Sabotax/Zdalne-ule/foldery pomocnicze/badania wytrzymalosci baterii/1.PNG

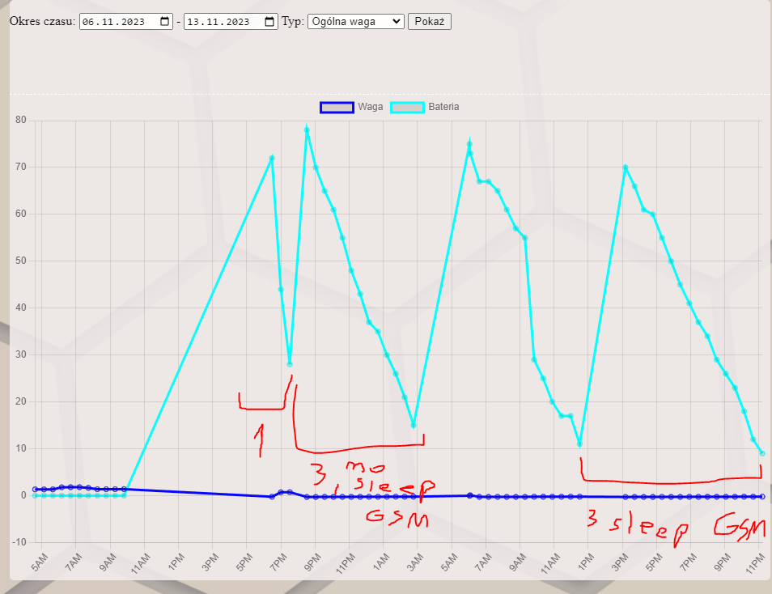
foldery pomocnicze/badania wytrzymalosci baterii/1.PNG
