Sabotax/Zdalne-ule/foldery pomocnicze/zdjecia readme/IMG_20230922_020804.jpg

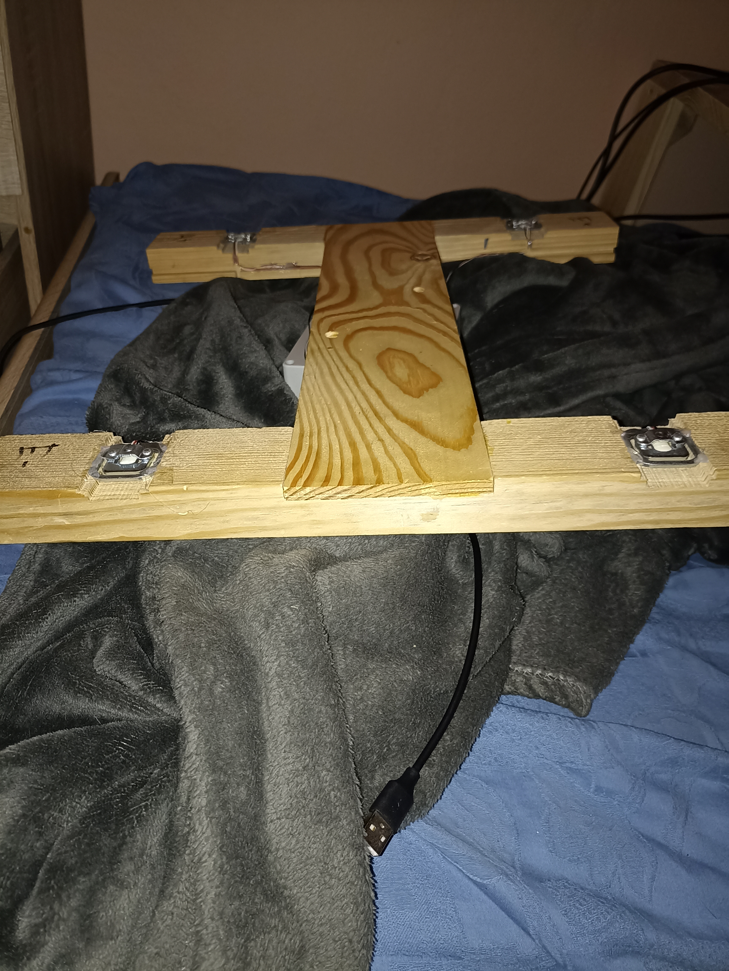
foldery pomocnicze/zdjecia readme/IMG_20230922_020804.jpg
