Sabotax/Zdalne-ule/kod_serwer/web/res/hex-pattern-1.jpg

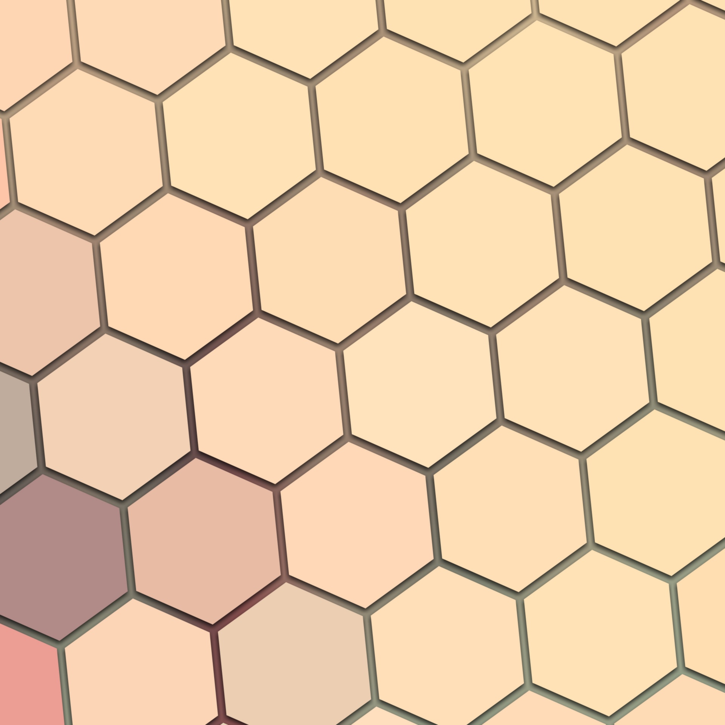
kod_serwer/web/res/hex-pattern-1.jpg
