Sabotax/Zdalne-ule/projekt PCB/esp-merged kicad/esp-merged_v1/2.png

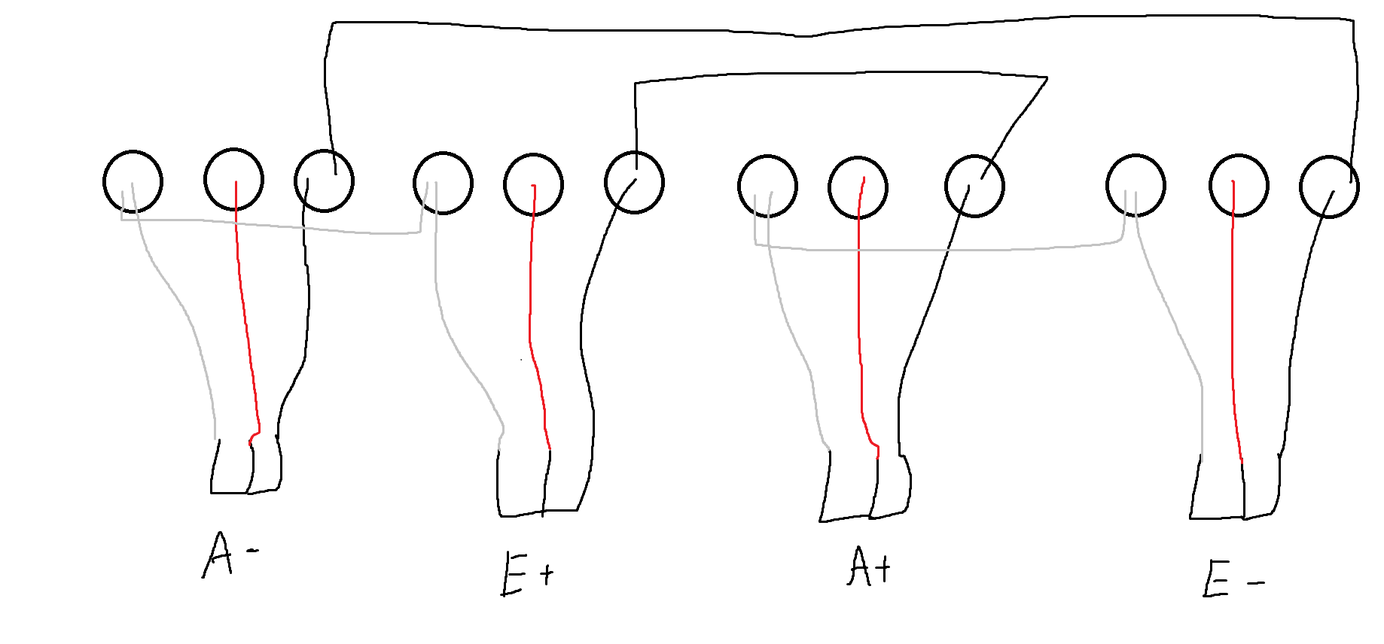
projekt PCB/esp-merged kicad/esp-merged_v1/2.png
