Sabotax/Zdalne-ule/przed czyszczeniem/arduino-esp-01-program.png

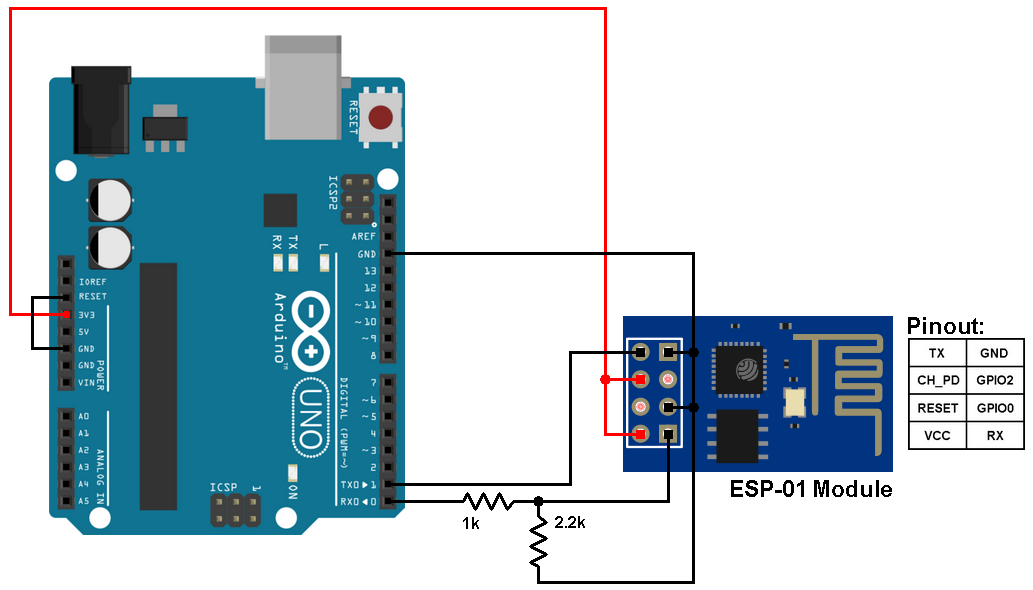
przed czyszczeniem/arduino-esp-01-program.png
