Sabotax/Zdalne-ule/przed czyszczeniem/programowanie wroom esp32/6662674700_1656869867.png

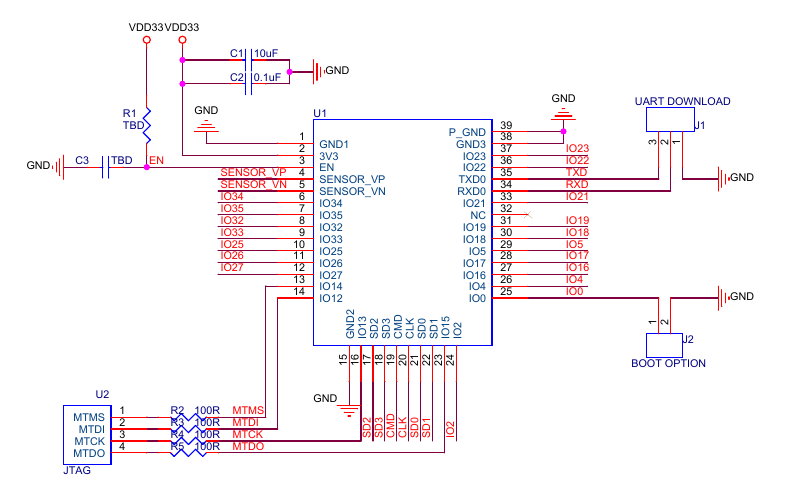
przed czyszczeniem/programowanie wroom esp32/6662674700_1656869867.png
