Sabotax/Zdalne-ule/przed czyszczeniem/programy/nauka/czujnik temperatury/schemat.PNG

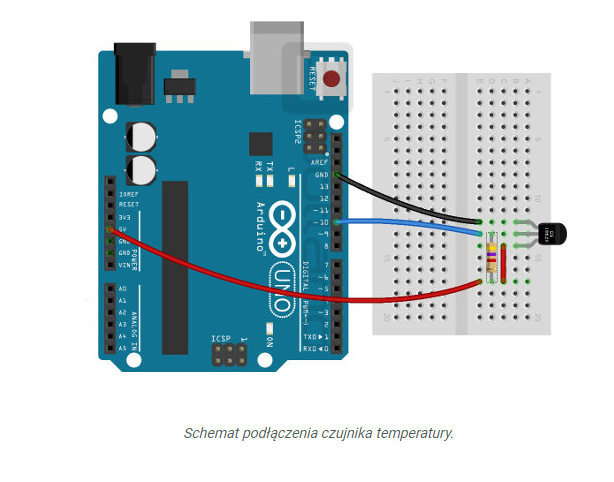
przed czyszczeniem/programy/nauka/czujnik temperatury/schemat.PNG
