Sabotax/Zdalne-ule/przed czyszczeniem/programy/nauka/ds3231_24_kwieciec/uklad_do_RST_esp_przez_pin_SQW_i_alarm.PNG

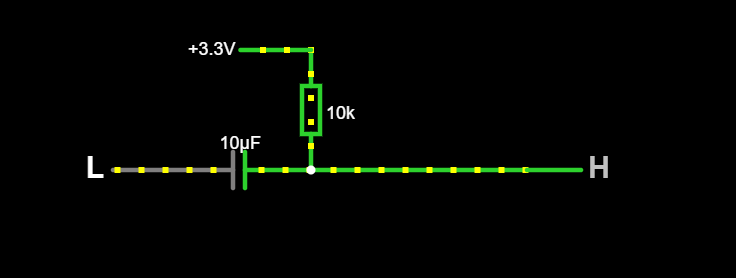
przed czyszczeniem/programy/nauka/ds3231_24_kwieciec/uklad_do_RST_esp_przez_pin_SQW_i_alarm.PNG
