Sabotax/Zdalne-ule/przed czyszczeniem/programy/nauka/esp8266 zewnetrzne do html serwer/flashowanie/dzien 2/sukceschyba..PNG

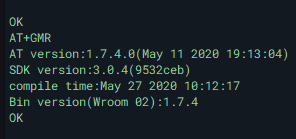
przed czyszczeniem/programy/nauka/esp8266 zewnetrzne do html serwer/flashowanie/dzien 2/sukceschyba..PNG
