Sabotax/Zdalne-ule/przed czyszczeniem/programy/nauka/esp8266 zewnetrzne do html serwer/flashowanie/error.PNG

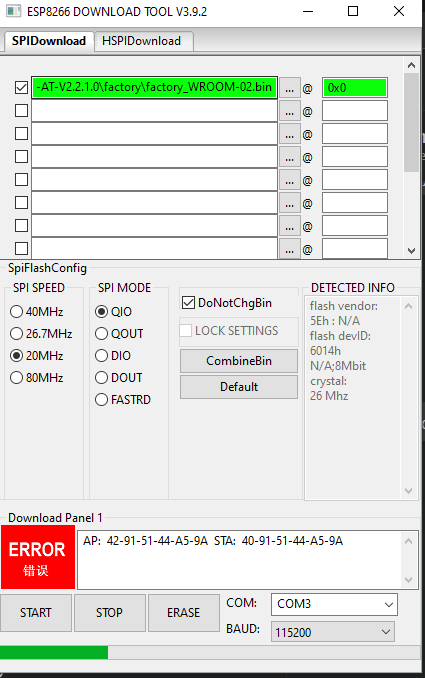
przed czyszczeniem/programy/nauka/esp8266 zewnetrzne do html serwer/flashowanie/error.PNG
