Sabotax/Zdalne-ule/przed czyszczeniem/programy/nauka/esp8266 zewnetrzne do html serwer/przyklad/FH5FWF4IRXSY8LC.png

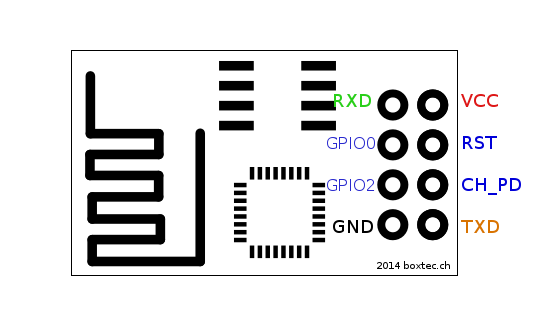
przed czyszczeniem/programy/nauka/esp8266 zewnetrzne do html serwer/przyklad/FH5FWF4IRXSY8LC.png
