Sabotax/Zdalne-ule/przed czyszczeniem/programy/nauka/esp8266 zewnetrzne do html serwer/przyklad/FW8CYZPIRXSZLLH.png

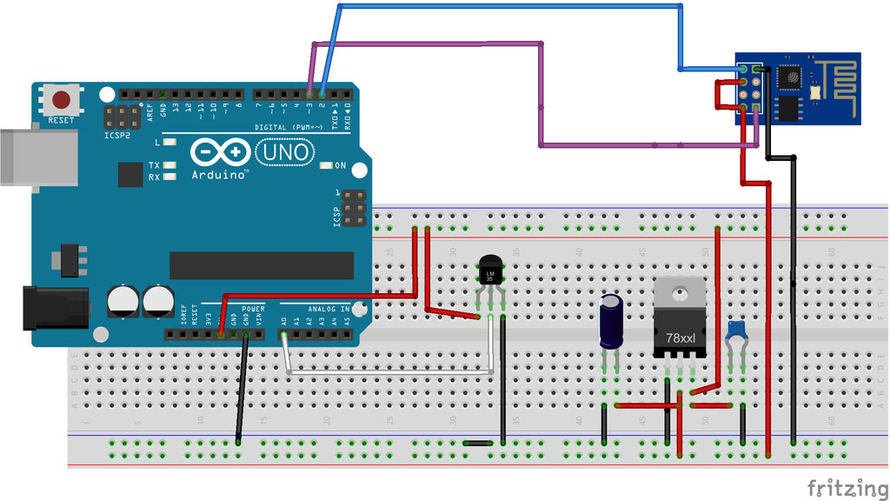
przed czyszczeniem/programy/nauka/esp8266 zewnetrzne do html serwer/przyklad/FW8CYZPIRXSZLLH.png
