Sabotax/Zdalne-ule/przed czyszczeniem/programy/nauka/esp8266 zewnetrzne do html serwer/przyklad/inne podlaczenie.PNG

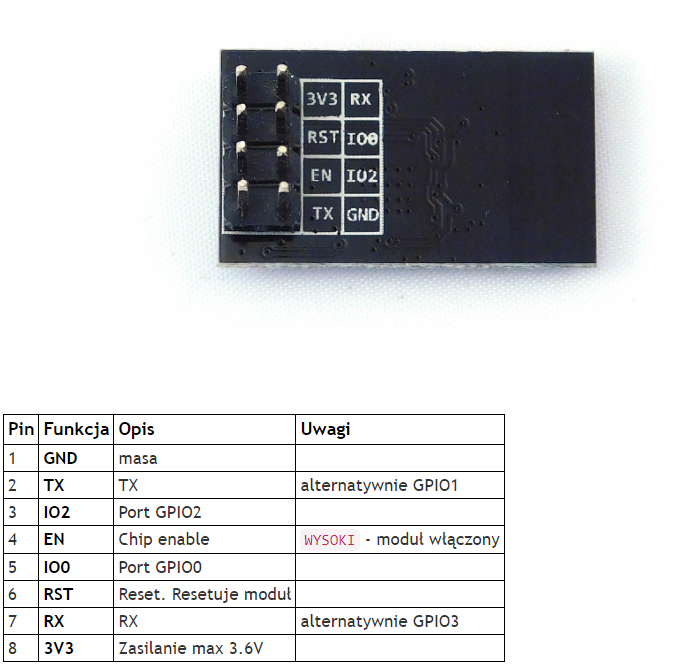
przed czyszczeniem/programy/nauka/esp8266 zewnetrzne do html serwer/przyklad/inne podlaczenie.PNG
