Sabotax/Zdalne-ule/przed czyszczeniem/programy/nauka/esp8266 zewnetrzne do html serwer/uzycie arduino jako posrednika/obwod.PNG

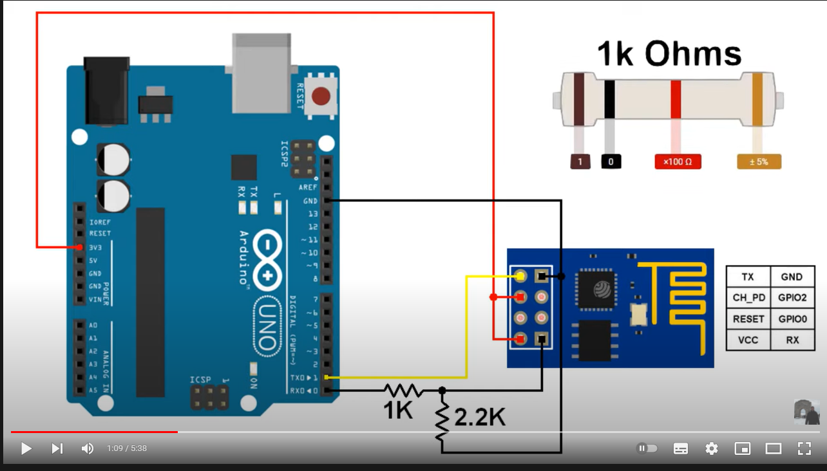
przed czyszczeniem/programy/nauka/esp8266 zewnetrzne do html serwer/uzycie arduino jako posrednika/obwod.PNG
