Sabotax/Zdalne-ule/przed czyszczeniem/programy/nauka/waga/2.PNG

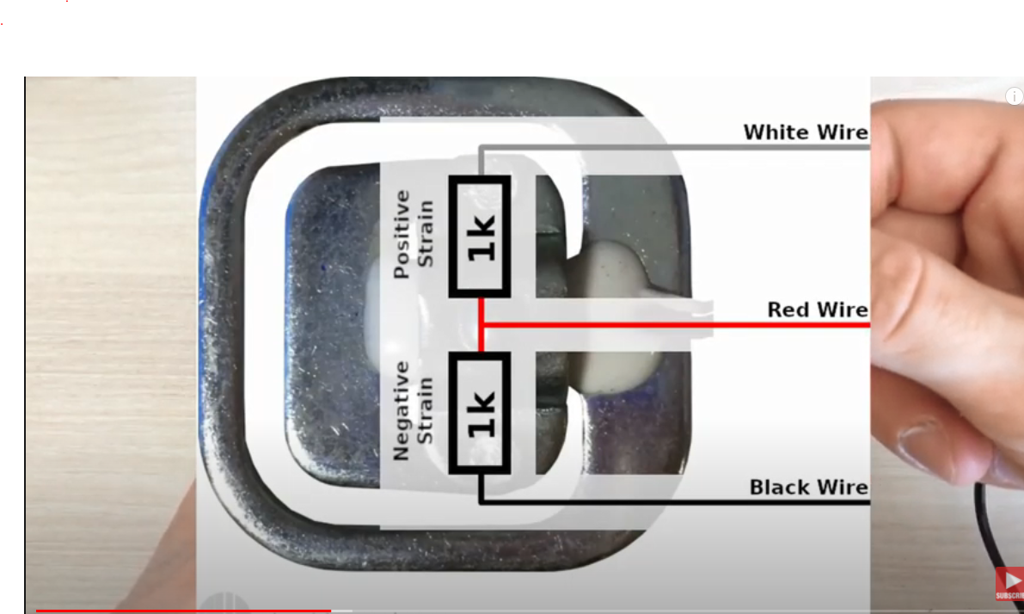
przed czyszczeniem/programy/nauka/waga/2.PNG
