Sabotax/Zdalne-ule/przed czyszczeniem/programy/nauka/waga/Przechwytywanie.PNG

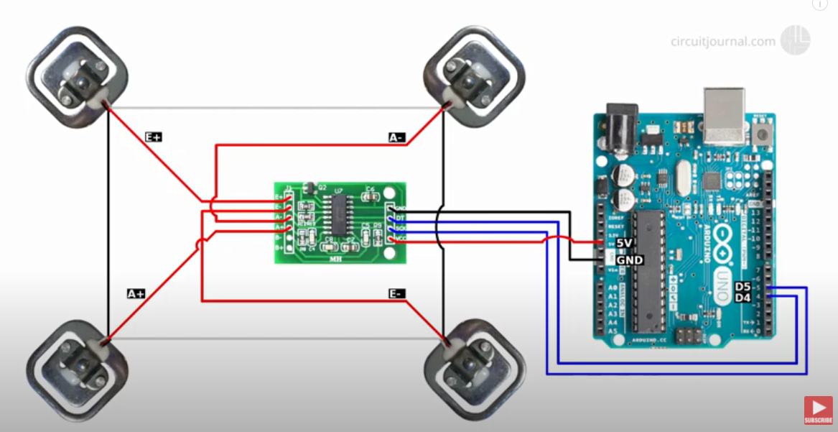
przed czyszczeniem/programy/nauka/waga/Przechwytywanie.PNG
