Sabotax/Zdalne-ule/przed czyszczeniem/programy/nauka/waga/schemat_zmodyfikowany.PNG

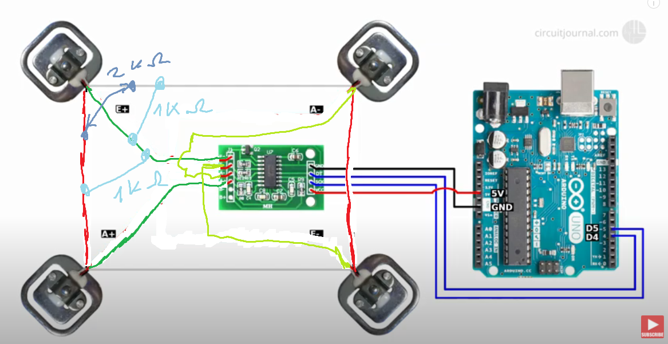
przed czyszczeniem/programy/nauka/waga/schemat_zmodyfikowany.PNG
