Sabotax/Zdalne-ule/przed czyszczeniem/programy/nauka_globalna_siec/oscyloskop/Bez_kondensatora.png

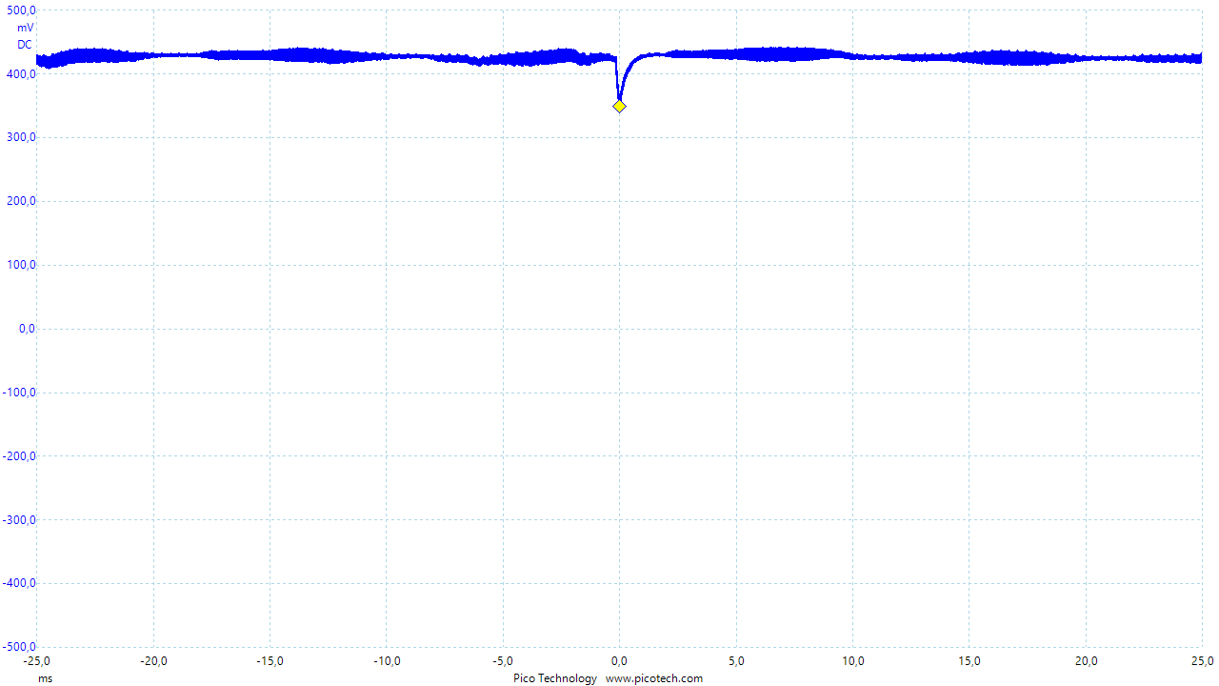
przed czyszczeniem/programy/nauka_globalna_siec/oscyloskop/Bez_kondensatora.png
