Sabotax/Zdalne-ule/przed czyszczeniem/programy/po przejsciu na BLE/v0.9/prawdopodobne ulozenie wagi.png

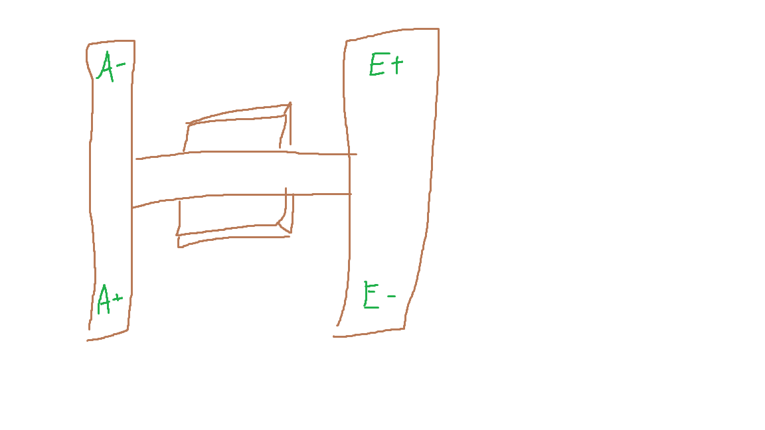
przed czyszczeniem/programy/po przejsciu na BLE/v0.9/prawdopodobne ulozenie wagi.png
