Sabotax/Zdalne-ule/przed czyszczeniem/rysunki/drugi_szkic.png

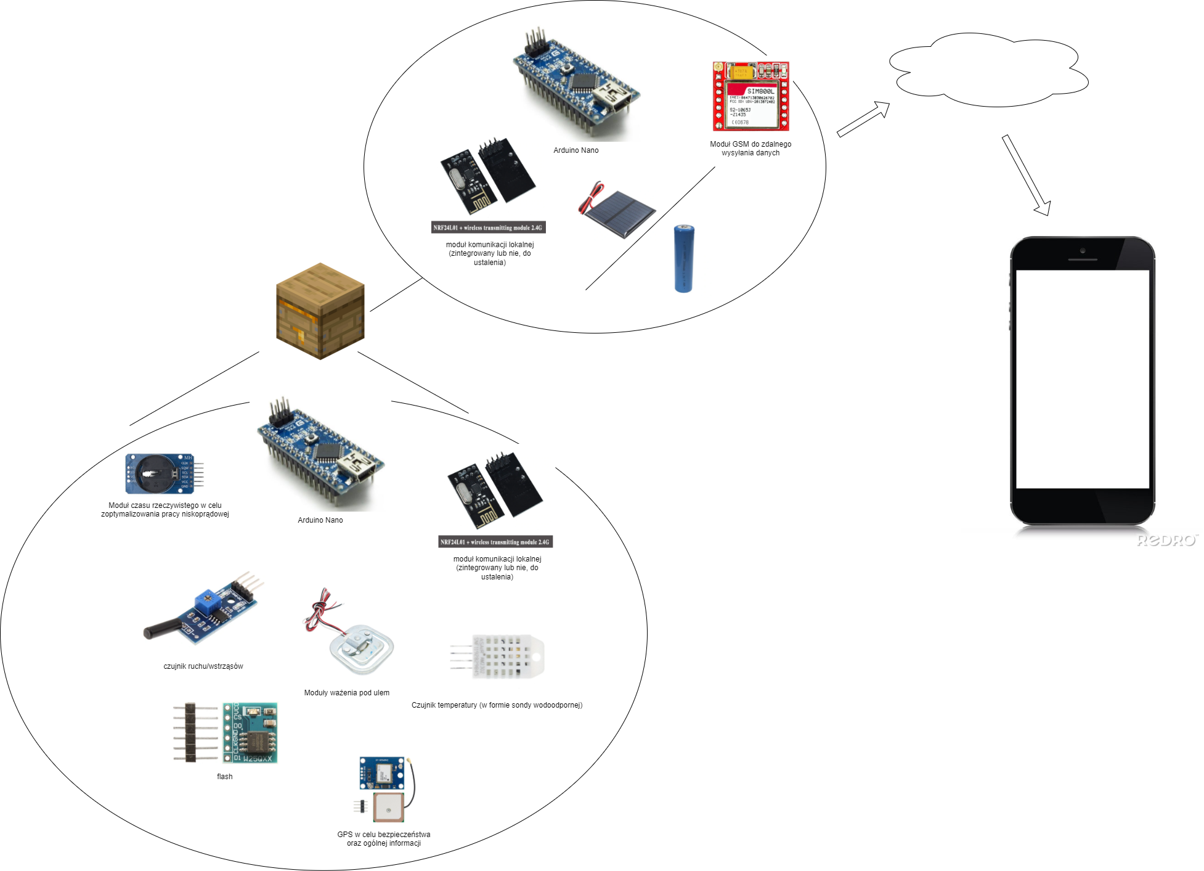
przed czyszczeniem/rysunki/drugi_szkic.png
