Sabotax/Zdalne-ule/foldery pomocnicze/rekordy rozmow z sim/debug komunikacji dla 2023-02-23.txt

epo________           _____       ______   ____________       _____________       
__  ___/______________(_)_____ ___  /   __  ___/_  /____  _______  /__(_)_____ 
_____ \_  _ \_  ___/_  /_  __ `/_  /    _____ \_  __/  / / /  __  /__  /_  __ \
____/ //  __/  /   _  / / /_/ /_  /     ____/ // /_ / /_/ // /_/ / _  / / /_/ /
/____/ \___//_/    /_/  \__,_/ /_/      /____/ \__/ \__,_/ \__,_/  /_/  \____/ 

Welcome to Serial Studio! To start, please select a COM port & baud rate in the
devices pane on the right. If serial connection is successful & incoming data is
interpreted correctly, this pane shall be automatically closed and the dashboard
shall be shown. Otherwise, you can use the console to find the source of your
problem.

Use the toolbar buttons to display the features that you want to use. If you
encounter a problem with Serial Studio, please report it at:

→ https://github.com/Serial-Studio/Serial-Studio/issues

You can also use the links in the "About" window. For documentation regarding
usage of Serial Studio & integration with your current MCU projects, please read
the wiki:

→ https://github.com/Serial-Studio/Serial-Studio/wiki

Tip: use the JSON Editor to create and edit Serial Studio project files.

00:21:53.371 -> ||
00:21:53.371 -> Wysylanie komendy AT: AT+CREG?
00:21:55.371 -> ||
00:21:55.371 -> Wysylanie komendy AT: AT+SAPBR=3,1,"Contype","GPRS"
00:21:57.372 -> ||
00:21:57.372 -> Wysylanie komendy AT: AT+SAPBR=3,1,"APN","internet"
00:21:59.372 -> ||
00:21:59.372 -> Wysylanie komendy AT: AT+SAPBR=3,1,"USER",""
00:22:01.371 -> ||
00:22:01.371 -> Wysylanie komendy AT: AT+SAPBR=3,1,"PWD",""
00:22:03.371 -> ||
00:22:03.371 -> Wysylanie komendy AT: AT+SAPBR=1,1
00:22:05.372 -> ||
00:22:05.372 -> Wysylanie komendy AT: AT+SAPBR=2,1
00:22:07.371 -> ||
00:22:07.371 -> Wysylanie komendy AT: AT+CNUM
00:22:11.372 -> ||
00:22:11.414 -> Wysylanie komendy AT: AT+CBC
00:22:15.412 -> |tempting to save data -0.27,1708733139;
00:22:15.478 -> Message appended
00:22:15.509 -> Wysylanie komendy AT: AT
00:22:19.507 -> |TTPINIT
00:22:26.507 -> |UN=0
00:22:30.508 -> ||
00:22:30.508 -> Wysylanie komendy AT: AT+CFUN=1,1
00:22:51.507 -> ||
00:22:51.507 -> Wysylanie komendy AT: AT+HTTPINIT
00:22:58.508 -> |CFUN=0
00:23:02.507 -> |FUN=1,1
00:23:23.507 -> |TPINIT
00:23:30.507 -> ||
00:23:30.507 -> Wysylanie komendy AT: AT+CFUN=0
00:23:34.507 -> ||
00:23:34.507 -> Wysylanie komendy AT: AT+CFUN=1,1
00:23:55.508 -> | komendy AT: AT+CFUN=0
00:23:55.511 -> Wysylanie komendy AT: AT+CSCLK=2
00:23:55.513 -> Czas spania: 1800 sekund
00:25:17.831 -> ets Jun  8 2016 00:22:57
00:25:17.831 -> 
00:25:17.831 -> rst:0x5 (DEEPSLEEP_RESET),boot:0x13 (SPI_FAST_FLASH_BOOT)
00:25:17.836 -> configsip: 0, SPIWP:0xee
00:25:17.839 -> clk_drv:0x00,q_drv:0x00,d_drv:0x00,cs0_drv:0x00,hd_drv:0x00,wp_drv:0x00
00:25:17.844 -> mode:DIO, clock div:1
00:25:17.847 -> load:0x3fff0030,len:1344
00:25:17.849 -> load:0x40078000,len:13516
00:25:17.852 -> load:0x40080400,len:3604
00:25:17.856 -> entry 0x400805f0
00:25:21.199 -> Wakeup caused by external signal using RTC_IO
00:25:21.243 -> Budzę GSM
00:25:21.243 -> Wysylanie komendy AT: AT
00:25:21.742 -> Wysylanie komendy AT: AT+CSCLK=0
00:25:27.743 -> ||
00:25:27.743 -> Wysylanie komendy AT: AT+CFUN=1
00:25:33.743 -> ||
00:25:35.124 -> Waiting a client connection to notify...
00:25:53.173 -> Przetwarzam input
00:25:53.173 -> rozkaz = 1
00:25:53.173 -> dane = 2024-02-23
00:25:53.175 -> Reading file: /2024-02-23.txt
00:25:53.319 -> Przetwarzam input
00:25:53.319 -> rozkaz = 2
00:25:53.319 -> dane = 
00:25:53.323 -> file 1
00:25:53.331 -> -
00:25:53.331 -> 0
00:25:53.331 -> .
00:25:53.331 -> 2
00:25:53.331 -> 6
00:25:53.331 -> ,
00:25:53.331 -> 1
00:25:53.331 -> 7
00:25:53.331 -> 0
00:25:53.331 -> 8
00:25:53.331 -> 6
00:25:53.334 -> 
00:25:53.334 -> 4
00:25:53.334 -> 6
00:25:53.334 -> 3
00:25:53.334 -> 9
00:25:53.334 -> 6
00:25:53.334 -> ;
00:25:53.334 -> debug incoming line -0.26,1708646396
00:25:53.337 -> debug waga build -
00:25:53.339 -> debug waga build 0
00:25:53.343 -> 
00:25:53.343 -> debug waga build .
00:25:53.343 -> debug waga build 2
00:25:53.346 -> debug waga build 6
00:25:53.346 -> debug switch 0
00:25:53.348 -> debug epoch build 1
00:25:53.351 -> debug epoch build 7
00:25:53.351 -> debug epoch build 0
00:25:53.354 -> debug epoch build 8
00:25:53.357 -> 
00:25:53.357 -> debug epoch build 6
00:25:53.357 -> debug epoch build 4
00:25:53.360 -> debug epoch build 6
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
00:27:20.047 -> 2
00:27:20.047 -> ,
00:27:20.050 -> 1
00:27:20.050 -> 7
00:27:20.050 -> 0
00:27:20.050 -> 8
00:27:20.050 -> 6
00:27:20.050 -> 9
00:27:20.050 -> 3
00:27:20.050 -> 3
00:27:20.050 -> 9
00:27:20.050 -> 2
00:27:20.052 -> ;
00:27:20.052 -> debug incoming line -0.22,1708693392
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
