Sabotax/Zdalne-ule/projekt PCB/esp-merged kicad/esp-merged_v1/fix na przycisk do zasypiania.PNG

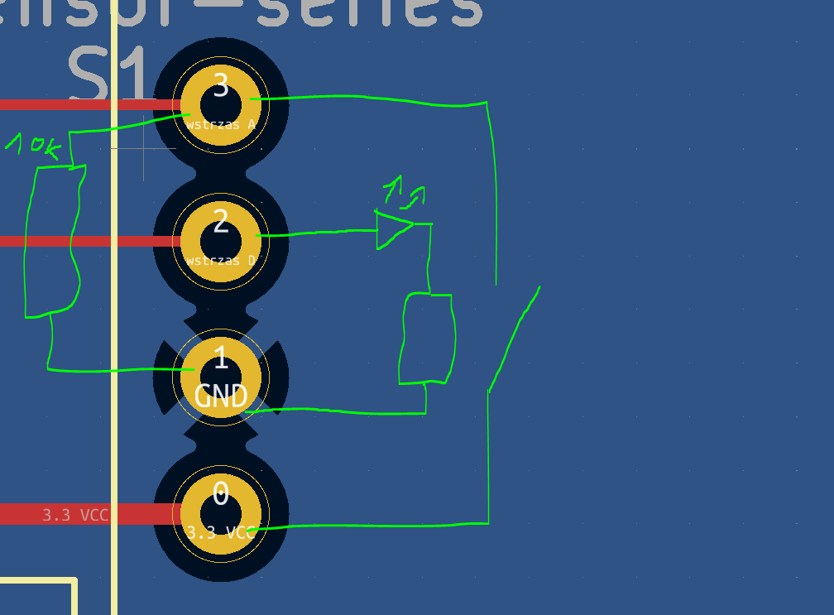
projekt PCB/esp-merged kicad/esp-merged_v1/fix na przycisk do zasypiania.PNG
