Sabotax/Zdalne-ule/przed czyszczeniem/programy/eksperymenty z wagą/kalibracjaWifi/kalibracjaWifi.ino

#include <HX711.h>
//#include "esp32-hal-cpu.h"
 
#define DOUT  16         //pin 3 Arduino i wyjście DAT czujnika
#define CLK  4           //pin 2 Arduino i wyjście CLK czujnika

 
HX711 loadcell;


#include <WiFi.h>

const char* ssid     = "NETIASPOT-C0D740";
const char* password = "9533f5tdu5av";

WiFiServer server(80);
 
void setup() {
  setCpuFrequencyMhz(80);
  Serial.begin(115200);
  Serial.println("HX711 - program kalibracyjny");

  Serial.println();
    Serial.print("Connecting to ");
    Serial.println(ssid);

    WiFi.begin(ssid, password);

    while (WiFi.status() != WL_CONNECTED) {
        delay(500);
        Serial.print(".");
    }

    Serial.println("");
    Serial.println("WiFi connected.");
    Serial.println("IP address: ");
    Serial.println(WiFi.localIP());
    
    server.begin();

  loadcell.begin(DOUT, CLK);
  loadcell.set_scale();
  loadcell.set_offset();
 
}

void loop() {
 
WiFiClient client = server.available();   // listen for incoming clients

  if (client) {                             // if you get a client,
    Serial.println("New Client.");           // print a message out the serial port
    String currentLine = "";                // make a String to hold incoming data from the client
    while (client.connected()) {            // loop while the client's connected
      if (client.available()) {             // if there's bytes to read from the client,
        char c = client.read();             // read a byte, then
        Serial.write(c);                    // print it out the serial monitor
        if (c == '\n') {                    // if the byte is a newline character

          // if the current line is blank, you got two newline characters in a row.
          // that's the end of the client HTTP request, so send a response:
          if (currentLine.length() == 0) {
            // HTTP headers always start with a response code (e.g. HTTP/1.1 200 OK)
            // and a content-type so the client knows what's coming, then a blank line:
            client.println("HTTP/1.1 200 OK");
            client.println("Content-type:text/html");
            client.println();

            // the content of the HTTP response follows the header:
            client.print("X: "+ String(loadcell.get_units(3)));
            //client.print("Click <a href=\"/L\">here</a> to turn the LED on pin 5 off.<br>");

            // The HTTP response ends with another blank line:
            client.println();
            // break out of the while loop:
            break;
          } else {    // if you got a newline, then clear currentLine:
            currentLine = "";
          }
        } else if (c != '\r') {  // if you got anything else but a carriage return character,
          currentLine += c;      // add it to the end of the currentLine
        }

        // Check to see if the client request was "GET /H" or "GET /L":
        if (currentLine.endsWith("GET /H")) {
          digitalWrite(5, HIGH);               // GET /H turns the LED on
        }
        if (currentLine.endsWith("GET /L")) {
          digitalWrite(5, LOW);                // GET /L turns the LED off
        }
      }
    }
    // close the connection:
    client.stop();
    Serial.println("Client Disconnected.");
  }

}
