Sabotax/Zdalne-ule/przed czyszczeniem/programy/nauka/czujnik wibracji/v2/v2.ino

#define digital_wstrzas 26
#define analog_wstrzas 25

RTC_DATA_ATTR int bootCount = 0;

void print_wakeup_reason(){
  esp_sleep_wakeup_cause_t wakeup_reason;

  wakeup_reason = esp_sleep_get_wakeup_cause();

  switch(wakeup_reason)
  {
    case ESP_SLEEP_WAKEUP_EXT0 : Serial.println("Wakeup caused by external signal using RTC_IO"); break;
    case ESP_SLEEP_WAKEUP_EXT1 : Serial.println("Wakeup caused by external signal using RTC_CNTL"); break;
    case ESP_SLEEP_WAKEUP_TIMER : Serial.println("Wakeup caused by timer"); break;
    case ESP_SLEEP_WAKEUP_TOUCHPAD : Serial.println("Wakeup caused by touchpad"); break;
    case ESP_SLEEP_WAKEUP_ULP : Serial.println("Wakeup caused by ULP program"); break;
    default : Serial.printf("Wakeup was not caused by deep sleep: %d\n",wakeup_reason); break;
  }
}
void setup() {
  // put your setup code here, to run once:
  Serial.begin(115200);
  delay(1000);
  pinMode(digital_wstrzas,INPUT);
  pinMode(analog_wstrzas,INPUT);

  ++bootCount;
  Serial.println("Boot number: " + String(bootCount));
  print_wakeup_reason();

  esp_sleep_enable_ext0_wakeup(GPIO_NUM_26, 0);

  Serial.println("Going to sleep now");
  delay(1000);
  esp_deep_sleep_start();
  Serial.println("This will never be printed");
}

void loop() {
  Serial.println(String(analogRead(analog_wstrzas))+"\t"+String(digitalRead(digital_wstrzas)));
  delay(10);
}
