Sabotax/Zdalne-ule/przed czyszczeniem/programy/eksperymenty z wagą/HX711_basic_example/HX711_basic_example.ino

#include "HX711.h"

// HX711 circuit wiring
const int LOADCELL_DOUT_PIN = 16;
const int LOADCELL_SCK_PIN = 4;

HX711 scale;

void setup() {
  Serial.begin(115200);
  scale.begin(LOADCELL_DOUT_PIN, LOADCELL_SCK_PIN);

  Serial.println("start");
}

void loop() {

  if (scale.is_ready()) {
    Serial.println("rdy");
    long reading = scale.read();
    Serial.print("HX711 reading: ");
    Serial.println(reading);
  } else {
    Serial.println("HX711 not found.");
  }

  delay(1000);
  
}
