Sabotax/Zdalne-ule/przed czyszczeniem/programy/nauka/ds3231_24_kwieciec/deep_sleep_simple_time/deep_sleep_simple_time.ino

/*
 * ESP8266 Deep sleep mode example
 * Rui Santos 
 * Complete Project Details https://randomnerdtutorials.com
 */
 
void setup() {
  Serial.begin(74880);
  Serial.setTimeout(2000);

  // Wait for serial to initialize.
  while(!Serial) { }
  
  // Deep sleep mode for 30 seconds, the ESP8266 wakes up by itself when GPIO 16 (D0 in NodeMCU board) is connected to the RESET pin
  Serial.println("I'm awake, but I'm going into deep sleep mode for 120 seconds");
  Serial.flush();
  ESP.deepSleep(120e6); 
  
  // Deep sleep mode until RESET pin is connected to a LOW signal (for example pushbutton or magnetic reed switch)
//  Serial.println("I'm awake, but I'm going into deep sleep mode until RESET pin is connected to a LOW signal");
//  ESP.deepSleep(0); 
}

void loop() {
}
