Sabotax/Zdalne-ule/przed czyszczeniem/programy/merged_slave_master/v2 kastracja dla testów/mergred_slave_master_v2/authData.h

// WiFi 
const char* ssid = /*"CGA2121_Tu7GnYu"*/ "NETIASPOT-C0D740" /*"INEA-1889_5G"*/ ;
const char* password = /*"mtyRdz7KZcEc9k2Ezw"*/ "9533f5tdu5av" /*"2RH4e5yx"*/;
const char* serverName = "http://lepotato-zdalneule.ddns.net/incomingData.php";

// Server details GSM
//const char server[] = "http://daniel.rozycki.student.put.poznan.pl";
const char server[] = "http://lepotato-zdalneule.ddns.net";
const char resource[] = "/incomingData.php";
const char serverAndResource[] = "http://lepotato-zdalneule.ddns.net/incomingData.php";
